Ace6Rings/MUSIC-PLAYER/CODE/NRF_AUDIO/src/modules/button_assignments.h

#ifndef _BUTTON_ASSIGNMENTS_H_
#define _BUTTON_ASSIGNMENTS_H_

#define BUTTON_NOT_ASSIGNED 0xFFFF


#define BUTTON_VOLUME_DOWN  820   //
#define BUTTON_VOLUME_UP    1640  // 
#define BUTTON_PLAY_PAUSE   2457  // 
#define BUTTON_4            3277  //
#define BUTTON_5            4000

#define ADC_TOLERANCE       150

#endif /* _BUTTON_ASSIGNMENTS_H_ */

#define BUTTON_5_GPIO_SAFE  ((gpio_pin_t)0xFF)
